glecuy/BionX32/Core/Inc/main.h

#define BlueLED_Pin GPIO_PIN_13
#define BlueLED_GPIO_Port GPIOC
#define Probe01_Pin GPIO_PIN_5
#define Probe01_GPIO_Port GPIOA
#define Hall_H1_Pin GPIO_PIN_6
#define Hall_H1_GPIO_Port GPIOA
#define Hall_H2_Pin GPIO_PIN_7
#define Hall_H2_GPIO_Port GPIOA
#define Hall_H3_Pin GPIO_PIN_0
#define Hall_H3_GPIO_Port GPIOB
